catdogmat/yevvle/firmware/main/display.cpp

// based on Demo Example from Good Display, available here: http://www.e-paper-display.com/download_detail/downloadsId=806.html
// Panel: GDEH0154D67 : http://www.e-paper-display.com/products_detail/productId=455.html
// Controller : SSD1681 : http://www.e-paper-display.com/download_detail/downloadsId=825.html
//
// Inspired on GxEPD2 by Author: Jean-Marc Zingg
// Library: https://github.com/ZinggJM/GxEPD2
//
// Fully rewriten for this project

#include "display.h"
#include "power.h"
#include "hardware.h"
#include "driver/gpio.h"
#include "driver/rtc_io.h"

// The display will remember the config and RAM between runs
// we can remember them and avoid expensive SPI calls
static RTC_DATA_ATTR struct DisplayState {
  bool initialized : 1 {false};
  bool fullMode : 1 {false};
  bool firstRefreshDone : 1 {false};
  bool darkBorder : 1 {false};
  bool inverted : 1 {false};
  bool postInvert : 1 {false};
  DisplayMode mode {DisplayMode::FULL};
} kState;

int RTC_IRAM_ATTR getSetDisplayMode() { return kState.mode; };

namespace {
  const SPISettings kSpiSettings{Display::kOverdriveSPI ? 26'666'666 : 20'000'000, MSBFIRST, SPI_MODE0};
}

SemaphoreHandle_t sSem = NULL;
void isr(void* ) {
  BaseType_t woken;
  gpio_intr_disable((gpio_num_t)HW::Display::Busy);
  xSemaphoreGiveFromISR(sSem, &woken);
}

void Display::_startTransfer()
{
  SPI.beginTransaction(kSpiSettings);
  gpio_set_level((gpio_num_t)HW::Display::Cs, LOW);
}
void Display::_endTransfer()
{
  gpio_set_level((gpio_num_t)HW::Display::Cs, HIGH);
  SPI.endTransaction();
}

void Display::_transfer(uint8_t value)
{
  SPI.write(value);
}

void Display::_transfer(const uint8_t* value, size_t size)
{
  SPI.writeBytes(value, size);
}

void Display::_transferCommand(uint8_t c)
{
  gpio_set_level((gpio_num_t)HW::Display::Dc, LOW);
  SPI.write(c);
  gpio_set_level((gpio_num_t)HW::Display::Dc, HIGH);
}

Display::Display() : Adafruit_GFX(WIDTH, HEIGHT) {
  // Set pins
  pinMode(HW::Display::Cs, OUTPUT);
  pinMode(HW::Display::Dc, OUTPUT);
  pinMode(HW::Display::Res, OUTPUT);
  pinMode(HW::Display::Busy, INPUT);

  digitalWrite(HW::Display::Cs, HIGH);
  digitalWrite(HW::Display::Dc, HIGH);
  digitalWrite(HW::Display::Res, HIGH);
  
  // Reset HW / Exit Deep Sleep
  if (rtc_gpio_is_valid_gpio((gpio_num_t)HW::Display::Res))
    rtc_gpio_hold_dis((gpio_num_t)HW::Display::Res);
  gpio_set_level((gpio_num_t)HW::Display::Res, LOW);
  delay(1);
  gpio_set_level((gpio_num_t)HW::Display::Res, HIGH); // THE HAT BOARD NEEDS output high
  //pinMode(HW::Display::Res, INPUT_PULLUP);
  if (rtc_gpio_is_valid_gpio((gpio_num_t)HW::Display::Res))
    rtc_gpio_hold_en((gpio_num_t)HW::Display::Res);

  // Display requires ISR service for busy pin
  gpio_intr_disable((gpio_num_t)HW::Display::Busy);
  gpio_install_isr_service(ESP_INTR_FLAG_LEVEL1);
  init();
}

void Display::init() {
  // This only needs to be done once
  if (kState.initialized)
    return;

  _startTransfer();
  _transferCommand(0x12); // SW reset all values to factory defaults
  _endTransfer();
  waitWhileBusy();

  _startTransfer();
  _transferCommand(0x01); // Driver output control
  _transfer(0xC7); // 0x0C7 is already the default
  _transfer(0b0);
  _transfer(0b000); // Gate scanning sequence, default 000
  // TODO: Can implement mirror Y feature with this bit 001

  if constexpr (kReduceBoosterTime) {
    // SSD1675B controller datasheet
    _transferCommand(0x0C); // BOOSTER_SOFT_START_CONTROL
    // Set the driving strength of GDR for all phases to maximun 0b111 -> 0xF
    // Set the minimum off time of GDR to minimum 0x4 (values below sould be same)
    _transfer(0xF4); // Phase1 Default value 0x8B
    _transfer(0xF4); // Phase2 Default value 0x9C
    _transfer(0xF4); // Phase3 Default value 0x96
    _transfer(0x00); // Duration of phases, Default 0xF = 0b00 11 11 (40ms Phase 1/2, 10ms Phase 3)
  }

  if constexpr (kFastUpdateTemp) {
    // Write 50ºC fixed temp (fastest update, but less quality)
    _transferCommand(0x1A);
    _transfer(0x32);
    _transfer(0x00);
  }

  // setRamAdressMode
  _transferCommand(0x11); // set ram entry mode
  _transfer(0b11);        //  0bYX adress mode (+1/-0), Default 0b11

  // Set initial refresh mode, will not change until first refresh
  _setRefreshMode(FULL);
  _endTransfer();

  kState.initialized = true;
}

void Display::_setCustomLut(const DisplayMode& mode) {
  auto& lut = [&] -> const LUT& {
    if (mode == GOOD)
      return SSD1681_LIGHTMYINK_CUSTOM_6_1;
    if (mode == QUICK)
      return SSD1681_LIGHTMYINK_CUSTOM_2_1;
    //if (mode == REPAIR)
    //  return SSD1681_LIGHTMYINK_REPAIR;
    return SSD1681_LIGHTMYINK_CUSTOM_6_1;
    // Other possible LUTS to use
    // auto& lut = SSD1681_WAVESHARE_1IN54_V2_LUT_FULL_REFRESH;
    // auto& lut = SSD1681_WAVESHARE_1IN54_V2_LUT_FAST_REFRESH;
    // auto& lut = SSD1681_WAVESHARE_1IN54_V2_LUT_FAST_REFRESH_KEEP;
  }();

  /* Always write main part of LUT register */
  _transferCommand(0x32);
  _transfer(lut.get().data(), 153);
  // End Option (EOPT)
  if (lut.eopt) {
    _transferCommand(0x3F); // set Lut option End
    _transfer(*lut.eopt);
  }
  /* GATE_DRIVING_VOLTAGE */
  if (lut.vgh) {
    _transferCommand(0x03);
    _transfer(*lut.vgh);
  }
  /* SRC_DRIVING_VOLTAGE */
  if (lut.vsh1_vsh2_vsl) {
    _transferCommand(0x04);
    _transfer(lut.vsh1_vsh2_vsl->data(), 3);
  }
  /* SET_VCOM_REG */
  if (lut.vcom) {
    _transferCommand(0x2c);
    _transfer(*lut.vcom);
  }
}

void Display::_setRamArea(const Rect& rect){
  auto& [x, y, w, h] = rect;
  _transferCommand(0x44);  // X start & end positions (Byte)
  _transfer(x >> 3);
  _transfer((x + w - 1) >> 3);
  _transferCommand(0x45); // Y start & end positions (Line)
  _transfer(y);
  _transfer(0);
  _transfer(y + h - 1);
  //_transfer(0); // No need to write this, default is 0
  _transferCommand(0x4e); // X start counter
  _transfer(x >> 3);
  _transferCommand(0x4f); // Y start counter
  _transfer(y);
  //_transfer(0); // No need to write this, default is 0
}

void Display::setRefreshMode(DisplayMode mode)
{
  if (kState.mode == mode)
    return;
  kState.mode = mode;

  // Can´t change the refresh mode until first frame is rendered
  if (!kState.firstRefreshDone)
    return;

  _startTransfer();
  _setRefreshMode(mode);
  _endTransfer();
}
DisplayMode Display::getRefreshMode() const
{
  return kState.mode;
}

void Display::_setRefreshMode(const DisplayMode& mode)
{
  constexpr auto kTurnOn = 0b11000000; // Enables oscillator & analog
  constexpr auto kLoadTemp = 0b00100000;
  constexpr auto kLoadLut = 0b00010000;
  constexpr auto kPartialMode = 0b00001000;
  constexpr auto kDisplay = 0b00000100;
  // constexpr auto kTurnOff = 0b00000011; // Disables oscillator & analog

  // Default modes FAST/FULL are loaded from the ROM
  bool romLut = mode == DisplayMode::FULL || mode == DisplayMode::FAST;

  // Build default updateCommand
  uint8_t updateCommand = kTurnOn; 
  if (romLut) {
    updateCommand |= kLoadLut;
  } else {
    _setCustomLut(mode);
  }
  if (mode != DisplayMode::FULL) {
    updateCommand |= kPartialMode;
  }
  if (!kFastUpdateTemp) {
    updateCommand |= kLoadTemp;
  }

  // If we are chaging from FULL to FAST/CUSTOM need to set
  // the display into 2 buffer mode again by triggering an update
  if ((mode == DisplayMode::FULL) ^ kState.fullMode && kState.firstRefreshDone) {
    _transferCommand(0x22);
    _transfer(updateCommand);
    _transferCommand(0x20);
    _endTransfer();
    waitWhileBusy();
    _startTransfer();
  }

  _transferCommand(0x22);
  _transfer(updateCommand | kDisplay);
  kState.fullMode = mode == DisplayMode::FULL;
}

void Display::refresh()
{
  if (!kState.firstRefreshDone) {
    // Draw the backbuffer as well on first refresh
    writeAll(true);
  }
  {
    auto powerLock = Power::Lock(Power::Flag::Display);
    _startTransfer();
    _transferCommand(0x20);
    _endTransfer();

    waitWhileBusy();
  }
  if (!kState.firstRefreshDone) {
    _startTransfer();
    _setRefreshMode(kState.mode);
    _endTransfer();
    kState.firstRefreshDone = true;
  }

  // After a refresh, finalize the display inversion
  if (kState.postInvert) {
    kState.postInvert = false;
    _startTransfer();
    _transferCommand(0x21); // RAM for Display Update
    _transfer(kState.inverted ? 0b10001000 : 0b0); // Set both front/backbuffer
    _endTransfer();
  }
}

void Display::waitWhileBusy() {
  sSem = xSemaphoreCreateBinary();

  static constexpr gpio_config_t busy_conf = {
    .pin_bit_mask = 1ULL << HW::Display::Busy,
    .mode = GPIO_MODE_INPUT,
    .pull_up_en = GPIO_PULLUP_DISABLE,
    .pull_down_en = GPIO_PULLDOWN_DISABLE,
    .intr_type = GPIO_INTR_LOW_LEVEL,
  };
  gpio_config(&busy_conf);
  // Setting the GPIO config reenables the interrupt

  // Set the wakeup on busy, in case tasks sleep the chip as well
  gpio_wakeup_enable((gpio_num_t)HW::Display::Busy, GPIO_INTR_LOW_LEVEL);
  esp_sleep_enable_gpio_wakeup();
  gpio_isr_handler_add((gpio_num_t)HW::Display::Busy, isr, (void*) 0);

  if (xSemaphoreTake(sSem, 10'000 / portTICK_PERIOD_MS) != pdTRUE) {
    ESP_LOGE("displ", "semaphore expired!");
  }

  gpio_isr_handler_remove((gpio_num_t)HW::Display::Busy);
  gpio_intr_disable((gpio_num_t)HW::Display::Busy);
  gpio_wakeup_disable((gpio_num_t)HW::Display::Busy);
  esp_sleep_disable_wakeup_source(ESP_SLEEP_WAKEUP_GPIO);

  vSemaphoreDelete(sSem);
}

void Display::setDarkBorder(bool dark) {
  if (kState.darkBorder == dark)
    return;
  _startTransfer();
  _transferCommand(0x3C); // BorderWavefrom
  _transfer(dark ? 0x02 : 0x05);
  _endTransfer();
  kState.darkBorder = dark;
}

void Display::setInverted(bool inverted) {
  if (kState.inverted == inverted)
    return;
  kState.inverted = inverted;
  _startTransfer();
  _transferCommand(0x21); // RAM for Display Update
  if (kState.firstRefreshDone) {
    _transfer(inverted ? 0b1000 : 0b10000000); // Only invert the frontbuffer
    kState.postInvert = true; // Queue the change for backbuffer
  } else {
    _transfer(inverted ? 0b10001000 : 0b0); // Set both front/backbuffer
  }
  _endTransfer();
}

void Display::rotate(Rect& rect) const
{
  auto& [x, y, w, h] = rect;
  switch (getRotation())
  {
    case 1:
      std::swap(x, y);
      std::swap(w, h);
      x = WIDTH - x - w;
      break;
    case 2:
      x = WIDTH - x - w;
      y = HEIGHT - y - h;
      break;
    case 3:
      std::swap(x, y);
      std::swap(w, h);
      y = HEIGHT - y - h;
      break;
  }
}

void Display::alignRect(Rect& rect) const
{
  rotate(rect);
  auto& [x, y, w, h] = rect;

  // Align
  x = x & ~7; // byte boundary
  w = WIDTH - x < w ? WIDTH - x : w; // limit
  h = HEIGHT - y < h ? HEIGHT - y : h; // limit

  w = (w + 7) & ~7; // byte boundary, bitmaps are padded

  w = x + w < WIDTH ? w : WIDTH - x; // limit
  h = y + h < HEIGHT ? h : HEIGHT - y; // limit
}

void Display::writeAlignedRect(const Rect& rect)
{
  _startTransfer();
  _setRamArea(rect);
  _transferCommand(0x24);
  auto xst = rect.x >> 3;
  for (auto i = 0; i < rect.h; i++)
  {
    auto yoffset = (rect.y + i) * WB_BITMAP;
    SPI.writeBytes(buffer + xst + yoffset, rect.w >> 3);
  }
  _endTransfer();
}

void Display::writeAlignedRectPacked(const uint8_t* ptr, const Rect& rect)
{
  _startTransfer();
  _setRamArea(rect);
  // ESP_LOGE("area","%p, %d %d %d %d, size %d", ptr, x, y, w, h, ((uint16_t)h) * w / 8);
  _transferCommand(0x24);
  SPI.writeBytes(ptr, ((uint16_t)rect.h * rect.w) >> 3);
  _endTransfer();
}

void Display::writeRect(Rect rect)
{
  alignRect(rect);
  writeAlignedRect(rect);
}

void Display::writeAllAndRefresh()
{
  writeAll();
  refresh();
 }

void Display::writeAll(bool backbuffer)
{
  _startTransfer();
  _setRamArea({0, 0, WIDTH, HEIGHT});
  _transferCommand(backbuffer ? 0x26 : 0x24);
  SPI.writeBytes(buffer, sizeof(buffer));
  _endTransfer();
}

void Display::hibernate()
{
  _startTransfer();
  _transferCommand(0x10); // change deep sleep mode
  _transfer(0b01);  // mode 1 (RAM reading allowed)
  // _transfer(0b11); // mode 2 (no RAM reading allowed) // Doesn't work... why?
  // _transfer(0b10); // mode 2 as well?
  _endTransfer();
}

Rect Display::getTextRect(const char * str, int16_t xc, int16_t yc) {
  int16_t x, y;
  uint16_t w, h;
  getTextBounds(str, xc < 0 ? cursor_x : xc, yc < 0 ? cursor_y : yc, &x, &y, &w, &h);
  return {static_cast<uint8_t>(x), static_cast<uint8_t>(y),
          static_cast<uint8_t>(w), static_cast<uint8_t>(h)};
}

void Display::drawPixel(int16_t x, int16_t y, uint16_t color)
{
  // check rotation, move pixel around if necessary
  switch (getRotation())
  {
    case 1:
      std::swap(x, y);
      x = WIDTH - x - 1;
      break;
    case 2:
      x = WIDTH - x - 1;
      y = HEIGHT - y - 1;
      break;
    case 3:
      std::swap(x, y);
      y = HEIGHT - y - 1;
      break;
  }
  auto& ptr = buffer[(x >> 3) + y * WB_BITMAP];
  auto mask = 1 << (7 - (x & 7));
  if (color)
    ptr |= mask;
  else
    ptr &= ~mask;
  // ptr = (ptr & ~mask) | (-(color != 0) & mask); // Alternative
}

/**************************************************************************/
/*!
   @brief  Speed optimized vertical line drawing
   @param  x      Line horizontal start point
   @param  y      Line vertical start point
   @param  h      Length of vertical line to be drawn, including first point
   @param  color  Color to fill with
*/
/**************************************************************************/
void Display::drawFastVLine(int16_t x, int16_t y, int16_t h,
                               uint16_t color) {

  if (h < 0) { // Convert negative heights to positive equivalent
    h *= -1;
    y -= h - 1;
    if (y < 0) {
      h += y;
      y = 0;
    }
  }

  // Edge rejection (no-draw if totally off canvas)
  if ((x < 0) || (x >= width()) || (y >= height()) || ((y + h - 1) < 0)) {
    return;
  }

  if (y < 0) { // Clip top
    h += y;
    y = 0;
  }
  if (y + h > height()) { // Clip bottom
    h = height() - y;
  }

  if (getRotation() == 0) {
    drawFastRawVLine(x, y, h, color);
  } else if (getRotation() == 1) {
    int16_t t = x;
    x = WIDTH - 1 - y;
    y = t;
    x -= h - 1;
    drawFastRawHLine(x, y, h, color);
  } else if (getRotation() == 2) {
    x = WIDTH - 1 - x;
    y = HEIGHT - 1 - y;

    y -= h - 1;
    drawFastRawVLine(x, y, h, color);
  } else if (getRotation() == 3) {
    int16_t t = x;
    x = y;
    y = HEIGHT - 1 - t;
    drawFastRawHLine(x, y, h, color);
  }
}

/**************************************************************************/
/*!
   @brief  Speed optimized horizontal line drawing
   @param  x      Line horizontal start point
   @param  y      Line vertical start point
   @param  w      Length of horizontal line to be drawn, including first point
   @param  color  Color to fill with
*/
/**************************************************************************/
void Display::drawFastHLine(int16_t x, int16_t y, int16_t w,
                               uint16_t color) {
  if (w < 0) { // Convert negative widths to positive equivalent
    w *= -1;
    x -= w - 1;
    if (x < 0) {
      w += x;
      x = 0;
    }
  }

  // Edge rejection (no-draw if totally off canvas)
  if ((y < 0) || (y >= height()) || (x >= width()) || ((x + w - 1) < 0)) {
    return;
  }

  if (x < 0) { // Clip left
    w += x;
    x = 0;
  }
  if (x + w >= width()) { // Clip right
    w = width() - x;
  }

  if (getRotation() == 0) {
    drawFastRawHLine(x, y, w, color);
  } else if (getRotation() == 1) {
    int16_t t = x;
    x = WIDTH - 1 - y;
    y = t;
    drawFastRawVLine(x, y, w, color);
  } else if (getRotation() == 2) {
    x = WIDTH - 1 - x;
    y = HEIGHT - 1 - y;

    x -= w - 1;
    drawFastRawHLine(x, y, w, color);
  } else if (getRotation() == 3) {
    int16_t t = x;
    x = y;
    y = HEIGHT - 1 - t;
    y -= w - 1;
    drawFastRawVLine(x, y, w, color);
  }
}

/**************************************************************************/
/*!
   @brief    Speed optimized vertical line drawing into the raw canvas buffer
   @param    x   Line horizontal start point
   @param    y   Line vertical start point
   @param    h   length of vertical line to be drawn, including first point
   @param    color   Binary (on or off) color to fill with
*/
/**************************************************************************/
void Display::drawFastRawVLine(int16_t x, int16_t y, int16_t h,
                                  uint16_t color) {
  // x & y already in raw (rotation 0) coordinates, no need to transform.
  uint8_t *ptr = &buffer[(x >> 3) + y * WB_BITMAP];

  if (color > 0) {
    uint8_t bit_mask = (0x80 >> (x & 7));
    for (int16_t i = 0; i < h; i++) {
      *ptr |= bit_mask;
      ptr += WB_BITMAP;
    }
  } else {
    uint8_t bit_mask = ~(0x80 >> (x & 7));
    for (int16_t i = 0; i < h; i++) {
      *ptr &= bit_mask;
      ptr += WB_BITMAP;
    }
  }
}

/**************************************************************************/
/*!
   @brief    Speed optimized horizontal line drawing into the raw canvas buffer
   @param    x   Line horizontal start point
   @param    y   Line vertical start point
   @param    w   length of horizontal line to be drawn, including first point
   @param    color   Binary (on or off) color to fill with
*/
/**************************************************************************/
void Display::drawFastRawHLine(int16_t x, int16_t y, int16_t w,
                                  uint16_t color) {
  // x & y already in raw (rotation 0) coordinates, no need to transform.
  uint8_t *ptr = &buffer[(x >> 3) + y * WB_BITMAP];
  size_t remainingWidthBits = w;

  // check to see if first byte needs to be partially filled
  if ((x & 7) > 0) {
    // create bit mask for first byte
    uint8_t startByteBitMask = 0x00;
    for (int8_t i = (x & 7); ((i < 8) && (remainingWidthBits > 0)); i++) {
      startByteBitMask |= (0x80 >> i);
      remainingWidthBits--;
    }
    if (color > 0) {
      *ptr |= startByteBitMask;
    } else {
      *ptr &= ~startByteBitMask;
    }

    ptr++;
  }

  // do the next remainingWidthBits bits
  if (remainingWidthBits > 0) {
    size_t remainingWholeBytes = remainingWidthBits >> 3;
    size_t lastByteBits = remainingWidthBits & 7;
    uint8_t wholeByteColor = color > 0 ? 0xFF : 0x00;

    memset(ptr, wholeByteColor, remainingWholeBytes);

    if (lastByteBits > 0) {
      uint8_t lastByteBitMask = 0x00;
      for (size_t i = 0; i < lastByteBits; i++) {
        lastByteBitMask |= (0x80 >> i);
      }
      ptr += remainingWholeBytes;

      if (color > 0) {
        *ptr |= lastByteBitMask;
      } else {
        *ptr &= ~lastByteBitMask;
      }
    }
  }
}
