catdogmat/yevvle/firmware/main/ble.cpp

/*
 * Licensed to the Apache Software Foundation (ASF) under one
 * or more contributor license agreements.  See the NOTICE file
 * distributed with this work for additional information
 * regarding copyright ownership.  The ASF licenses this file
 * to you under the Apache License, Version 2.0 (the
 * "License"); you may not use this file except in compliance
 * with the License.  You may obtain a copy of the License at
 *
 *  http://www.apache.org/licenses/LICENSE-2.0
 *
 * Unless required by applicable law or agreed to in writing,
 * software distributed under the License is distributed on an
 * "AS IS" BASIS, WITHOUT WARRANTIES OR CONDITIONS OF ANY
 * KIND, either express or implied.  See the License for the
 * specific language governing permissions and limitations
 * under the License.
 */

#include <assert.h>
#include <stdio.h>
#include <string.h>
#include "host/ble_hs.h"
#include "host/ble_uuid.h"
#include "services/gap/ble_svc_gap.h"
#include "services/gatt/ble_svc_gatt.h"

#include "nimble/ble.h"
#include "modlog/modlog.h"

#define TAG "NimBLE"

/* Heart-rate configuration */
#define GATT_HRS_UUID                           0x180D
#define GATT_HRS_MEASUREMENT_UUID               0x2A37
#define GATT_HRS_BODY_SENSOR_LOC_UUID           0x2A38
#define GATT_DEVICE_INFO_UUID                   0x180A
#define GATT_MANUFACTURER_NAME_UUID             0x2A29
#define GATT_MODEL_NUMBER_UUID                  0x2A24

extern uint16_t hrs_hrm_handle;

struct ble_hs_cfg;
struct ble_gatt_register_ctxt;

void gatt_svr_register_cb(struct ble_gatt_register_ctxt *ctxt, void *arg);
int gatt_svr_init(void);

static const char *manuf_name = "Apache Mynewt ESP32 devkitC";
static const char *model_num = "Mynewt HR Sensor demo";
uint16_t hrs_hrm_handle;

static int
gatt_svr_chr_access_heart_rate(uint16_t conn_handle, uint16_t attr_handle,
                               struct ble_gatt_access_ctxt *ctxt, void *arg);

static int
gatt_svr_chr_access_device_info(uint16_t conn_handle, uint16_t attr_handle,
                                struct ble_gatt_access_ctxt *ctxt, void *arg);

static const auto uuid_hrs_measurement = BLE_UUID16_DECLARE(GATT_HRS_MEASUREMENT_UUID);
static const auto uuid_hrs_loc = BLE_UUID16_DECLARE(GATT_HRS_BODY_SENSOR_LOC_UUID);

static const ble_gatt_chr_def hrs_chr_def[] = {
    {
        /* Characteristic: Heart-rate measurement */
        .uuid = uuid_hrs_measurement,
        .access_cb = gatt_svr_chr_access_heart_rate,
        .flags = BLE_GATT_CHR_F_NOTIFY,
        .val_handle = &hrs_hrm_handle,
    }, {
        /* Characteristic: Body sensor location */
        .uuid = uuid_hrs_loc,
        .access_cb = gatt_svr_chr_access_heart_rate,
        .flags = BLE_GATT_CHR_F_READ,
    }, {
        0, /* No more characteristics in this service */
    }
};
static const ble_gatt_chr_def device_chr_def[] = {
    {
        /* Characteristic: * Manufacturer name */
        .uuid = BLE_UUID16_DECLARE(GATT_MANUFACTURER_NAME_UUID),
        .access_cb = gatt_svr_chr_access_device_info,
        .flags = BLE_GATT_CHR_F_READ,
    }, {
        /* Characteristic: Model number string */
        .uuid = BLE_UUID16_DECLARE(GATT_MODEL_NUMBER_UUID),
        .access_cb = gatt_svr_chr_access_device_info,
        .flags = BLE_GATT_CHR_F_READ,
    }, {
        0, /* No more characteristics in this service */
    },
};
static const ble_gatt_svc_def gatt_svr_svcs[] = {
    {
        /* Service: Heart-rate */
        .type = BLE_GATT_SVC_TYPE_PRIMARY,
        .uuid = BLE_UUID16_DECLARE(GATT_HRS_UUID),
        .characteristics = hrs_chr_def
    },
    {
        /* Service: Device Information */
        .type = BLE_GATT_SVC_TYPE_PRIMARY,
        .uuid = BLE_UUID16_DECLARE(GATT_DEVICE_INFO_UUID),
        .characteristics = device_chr_def
    },
    {
        0, /* No more services */
    },
};

static int
gatt_svr_chr_access_heart_rate(uint16_t conn_handle, uint16_t attr_handle,
                               struct ble_gatt_access_ctxt *ctxt, void *arg)
{
    /* Sensor location, set to "Chest" */
    static uint8_t body_sens_loc = 0x01;
    uint16_t uuid;
    int rc;

    uuid = ble_uuid_u16(ctxt->chr->uuid);

    if (uuid == GATT_HRS_BODY_SENSOR_LOC_UUID) {
        rc = os_mbuf_append(ctxt->om, &body_sens_loc, sizeof(body_sens_loc));

        return rc == 0 ? 0 : BLE_ATT_ERR_INSUFFICIENT_RES;
    }

    assert(0);
    return BLE_ATT_ERR_UNLIKELY;
}

static int
gatt_svr_chr_access_device_info(uint16_t conn_handle, uint16_t attr_handle,
                                struct ble_gatt_access_ctxt *ctxt, void *arg)
{
    uint16_t uuid;
    int rc;

    uuid = ble_uuid_u16(ctxt->chr->uuid);

    if (uuid == GATT_MODEL_NUMBER_UUID) {
        rc = os_mbuf_append(ctxt->om, model_num, strlen(model_num));
        return rc == 0 ? 0 : BLE_ATT_ERR_INSUFFICIENT_RES;
    }

    if (uuid == GATT_MANUFACTURER_NAME_UUID) {
        rc = os_mbuf_append(ctxt->om, manuf_name, strlen(manuf_name));
        return rc == 0 ? 0 : BLE_ATT_ERR_INSUFFICIENT_RES;
    }

    assert(0);
    return BLE_ATT_ERR_UNLIKELY;
}

void
gatt_svr_register_cb(struct ble_gatt_register_ctxt *ctxt, void *arg)
{
    char buf[BLE_UUID_STR_LEN];

    switch (ctxt->op) {
    case BLE_GATT_REGISTER_OP_SVC:
        ESP_LOGE(TAG, "registered service %s with handle=%d",
                    ble_uuid_to_str(ctxt->svc.svc_def->uuid, buf),
                    ctxt->svc.handle);
        break;

    case BLE_GATT_REGISTER_OP_CHR:
        ESP_LOGE(TAG, "registering characteristic %s with "
                    "def_handle=%d val_handle=%d\n",
                    ble_uuid_to_str(ctxt->chr.chr_def->uuid, buf),
                    ctxt->chr.def_handle,
                    ctxt->chr.val_handle);
        break;

    case BLE_GATT_REGISTER_OP_DSC:
        ESP_LOGE(TAG, "registering descriptor %s with handle=%d\n",
                    ble_uuid_to_str(ctxt->dsc.dsc_def->uuid, buf),
                    ctxt->dsc.handle);
        break;

    default:
        assert(0);
        break;
    }
}

int
gatt_svr_init(void)
{
    int rc;

    ble_svc_gap_init();
    ble_svc_gatt_init();

    rc = ble_gatts_count_cfg(gatt_svr_svcs);
    if (rc != 0) {
        return rc;
    }

    rc = ble_gatts_add_svcs(gatt_svr_svcs);
    if (rc != 0) {
        return rc;
    }

    return 0;
}

#include "esp_log.h"
#include "nvs_flash.h"
#include "freertos/FreeRTOSConfig.h"
/* BLE */
#include "nimble/nimble_port.h"
#include "nimble/nimble_port_freertos.h"
#include "host/ble_hs.h"
#include "host/util/util.h"
#include "console/console.h"
#include "services/gap/ble_svc_gap.h"

static TimerHandle_t blehr_tx_timer;

static bool notify_state;

static uint16_t conn_handle;

static const char *device_name = "MyWatch";

static int blehr_gap_event(struct ble_gap_event *event, void *arg);

static uint8_t blehr_addr_type;

/* Variable to simulate heart beats */
static uint8_t heartrate = 90;


/*
 * Enables advertising with parameters:
 *     o General discoverable mode
 *     o Undirected connectable mode
 */
static void
blehr_advertise(void)
{
    struct ble_gap_adv_params adv_params;
    struct ble_hs_adv_fields fields;
    int rc;

    /*
     *  Set the advertisement data included in our advertisements:
     *     o Flags (indicates advertisement type and other general info)
     *     o Advertising tx power
     *     o Device name
     */
    memset(&fields, 0, sizeof(fields));

    /*
     * Advertise two flags:
     *      o Discoverability in forthcoming advertisement (general)
     *      o BLE-only (BR/EDR unsupported)
     */
    fields.flags = BLE_HS_ADV_F_DISC_GEN |
                   BLE_HS_ADV_F_BREDR_UNSUP;

    /*
     * Indicate that the TX power level field should be included; have the
     * stack fill this value automatically.  This is done by assigning the
     * special value BLE_HS_ADV_TX_PWR_LVL_AUTO.
     */
    fields.tx_pwr_lvl_is_present = 1;
    fields.tx_pwr_lvl = BLE_HS_ADV_TX_PWR_LVL_AUTO;

    fields.name = (uint8_t *)device_name;
    fields.name_len = strlen(device_name);
    fields.name_is_complete = 1;

    rc = ble_gap_adv_set_fields(&fields);
    if (rc != 0) {
        ESP_LOGE(TAG, "error setting advertisement data; rc=%d\n", rc);
        return;
    }

    /* Begin advertising */
    memset(&adv_params, 0, sizeof(adv_params));
    adv_params.conn_mode = BLE_GAP_CONN_MODE_UND;
    adv_params.disc_mode = BLE_GAP_DISC_MODE_GEN;
    rc = ble_gap_adv_start(blehr_addr_type, NULL, BLE_HS_FOREVER,
                           &adv_params, blehr_gap_event, NULL);
    if (rc != 0) {
        ESP_LOGE(TAG, "error enabling advertisement; rc=%d\n", rc);
        return;
    }
}

static void
blehr_tx_hrate_stop(void)
{
    xTimerStop( blehr_tx_timer, 1000 / portTICK_PERIOD_MS );
}

/* Reset heart rate measurement */
static void
blehr_tx_hrate_reset(void)
{
    int rc;

    if (xTimerReset(blehr_tx_timer, 1000 / portTICK_PERIOD_MS ) == pdPASS) {
        rc = 0;
    } else {
        rc = 1;
    }

    assert(rc == 0);

}

/* This function simulates heart beat and notifies it to the client */
static void
blehr_tx_hrate(TimerHandle_t ev)
{
    static uint8_t hrm[2];
    int rc;
    struct os_mbuf *om;

    if (!notify_state) {
        blehr_tx_hrate_stop();
        heartrate = 90;
        return;
    }

    hrm[0] = 0x06; /* contact of a sensor */
    hrm[1] = heartrate; /* storing dummy data */

    /* Simulation of heart beats */
    heartrate++;
    if (heartrate == 160) {
        heartrate = 90;
    }

    om = ble_hs_mbuf_from_flat(hrm, sizeof(hrm));
    rc = ble_gatts_notify_custom(conn_handle, hrs_hrm_handle, om);

    assert(rc == 0);

    blehr_tx_hrate_reset();
}

static int
blehr_gap_event(struct ble_gap_event *event, void *arg)
{
    switch (event->type) {
    case BLE_GAP_EVENT_CONNECT:
        /* A new connection was established or a connection attempt failed */
        ESP_LOGE(TAG, "connection %s; status=%d",
                    event->connect.status == 0 ? "established" : "failed",
                    event->connect.status);

        if (event->connect.status != 0) {
            /* Connection failed; resume advertising */
            blehr_advertise();
        }
        conn_handle = event->connect.conn_handle;
        break;

    case BLE_GAP_EVENT_DISCONNECT:
        ESP_LOGE(TAG, "disconnect; reason=%d", event->disconnect.reason);

        /* Connection terminated; resume advertising */
        blehr_advertise();
        break;

    case BLE_GAP_EVENT_ADV_COMPLETE:
        ESP_LOGE(TAG, "adv complete");
        blehr_advertise();
        break;

    case BLE_GAP_EVENT_SUBSCRIBE:
        ESP_LOGE(TAG, "subscribe event; cur_notify=%d\n value handle; "
                    "val_handle=%d",
                    event->subscribe.cur_notify, hrs_hrm_handle);
        if (event->subscribe.attr_handle == hrs_hrm_handle) {
            notify_state = event->subscribe.cur_notify;
            blehr_tx_hrate_reset();
        } else if (event->subscribe.attr_handle != hrs_hrm_handle) {
            notify_state = event->subscribe.cur_notify;
            blehr_tx_hrate_stop();
        }
        ESP_LOGI("BLE_GAP_SUBSCRIBE_EVENT", "conn_handle from subscribe=%d", conn_handle);
        break;

    case BLE_GAP_EVENT_MTU:
        ESP_LOGE(TAG, "mtu update event; conn_handle=%d mtu=%d\n",
                    event->mtu.conn_handle,
                    event->mtu.value);
        break;

    }

    return 0;
}

static void blehr_on_sync(void)
{
    int rc;

    rc = ble_hs_id_infer_auto(0, &blehr_addr_type);
    assert(rc == 0);

    uint8_t a[6] = {0};
    rc = ble_hs_id_copy_addr(blehr_addr_type, a, NULL);

    ESP_LOGE(TAG, "Device Address: %x:%x:%x:%x:%x:%x", a[0], a[1], a[2], a[3], a[4], a[5]);

    /* Begin advertising */
    blehr_advertise();
}

static void blehr_on_reset(int reason)
{
    ESP_LOGE(TAG, "Resetting state; reason=%d", reason);
}

void blehr_host_task(void *param)
{
    ESP_LOGI(TAG, "BLE Host Task Started");
    /* This function will return only when nimble_port_stop() is executed */
    nimble_port_run();

    nimble_port_freertos_deinit();
}

void ble_main(void)
{
    int rc;

    /* Initialize NVS — it is used to store PHY calibration data */
    esp_err_t ret = nvs_flash_init();
    if (ret == ESP_ERR_NVS_NO_FREE_PAGES || ret == ESP_ERR_NVS_NEW_VERSION_FOUND) {
        ESP_ERROR_CHECK(nvs_flash_erase());
        ret = nvs_flash_init();
    }
    ESP_ERROR_CHECK(ret);

    ret = nimble_port_init();
    if (ret != ESP_OK) {
        ESP_LOGE(TAG, "Failed to init nimble %d", ret);
        return;
    }

    /* Initialize the NimBLE host configuration */
    ble_hs_cfg.sync_cb = blehr_on_sync;
    ble_hs_cfg.reset_cb = blehr_on_reset;

    /* name, period/time,  auto reload, timer ID, callback */
    blehr_tx_timer = xTimerCreate("blehr_tx_timer", pdMS_TO_TICKS(1000), pdTRUE, (void *)0, blehr_tx_hrate);

    rc = gatt_svr_init();
    assert(rc == 0);

    /* Set the default device name */
    rc = ble_svc_gap_device_name_set(device_name);
    assert(rc == 0);

    /* Start the task */
    nimble_port_freertos_init(blehr_host_task);
}
