catdogmat/yevvle/firmware/main/secrets.h

#pragma once

#include "radio.h"

#include <string.h>
#include <vector>

struct WifiConfig {
    std::string mSsid, mPswd;
};
using WifiNetworks = std::vector<WifiConfig>;

extern const WifiNetworks kWifiNetworks;
extern const std::vector<Signal::Group> kSignals;
